lonesoulsurfer/Groove-Box-Drum-Machine/KiCad - Front Panel/Drum Kid - Front Panel.png

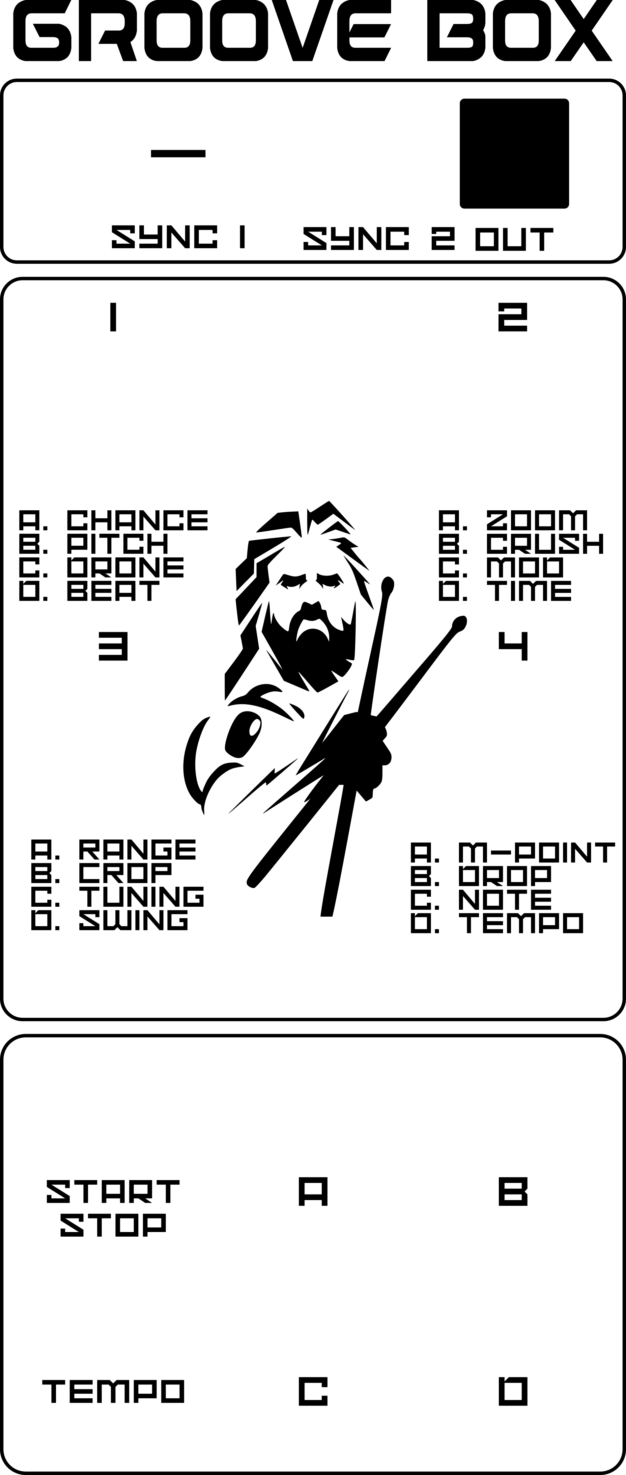
KiCad - Front Panel/Drum Kid - Front Panel.png
